phillycheeseman/particle/Proto Insert Two Layer/IMG_5750.jpeg

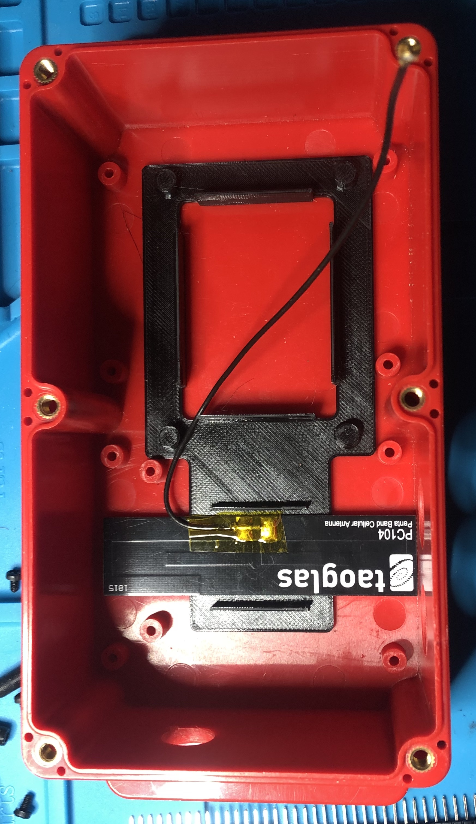
Proto Insert Two Layer/IMG_5750.jpeg
