phillycheeseman/particle/Proto Insert Two Layer/IMG_5751.jpeg

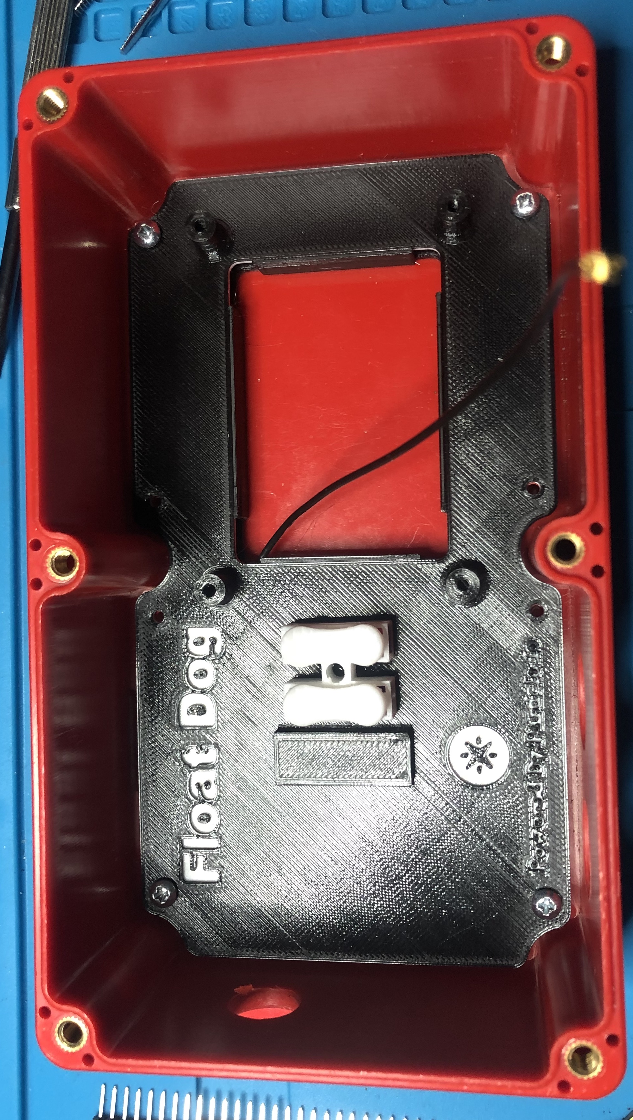
Proto Insert Two Layer/IMG_5751.jpeg
