phillycheeseman/particle/Proto Insert Two Layer/IMG_5753.jpeg

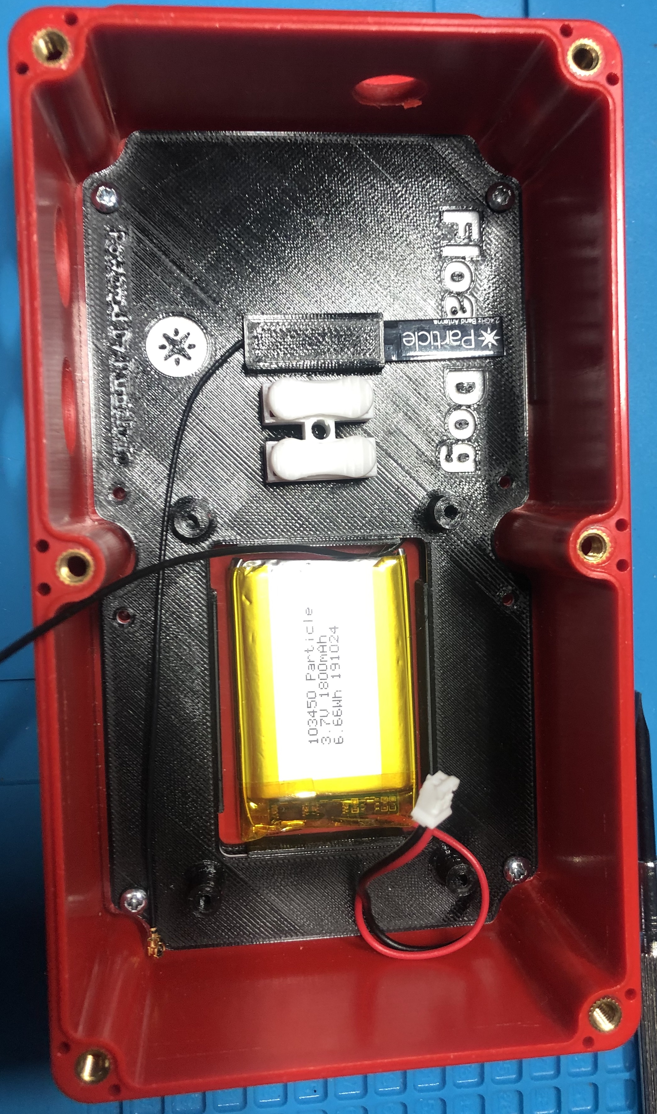
Proto Insert Two Layer/IMG_5753.jpeg
