phillycheeseman/particle/Proto Insert Two Layer/IMG_5755.jpeg

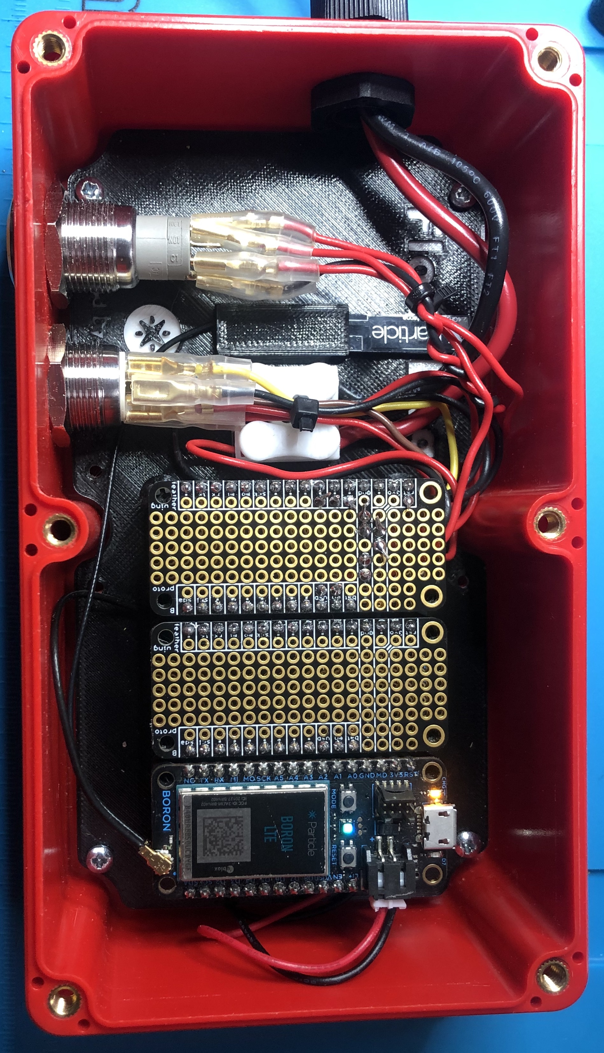
Proto Insert Two Layer/IMG_5755.jpeg
