phillycheeseman/particle/Proto Insert Two Layer/IMG_5757.jpeg

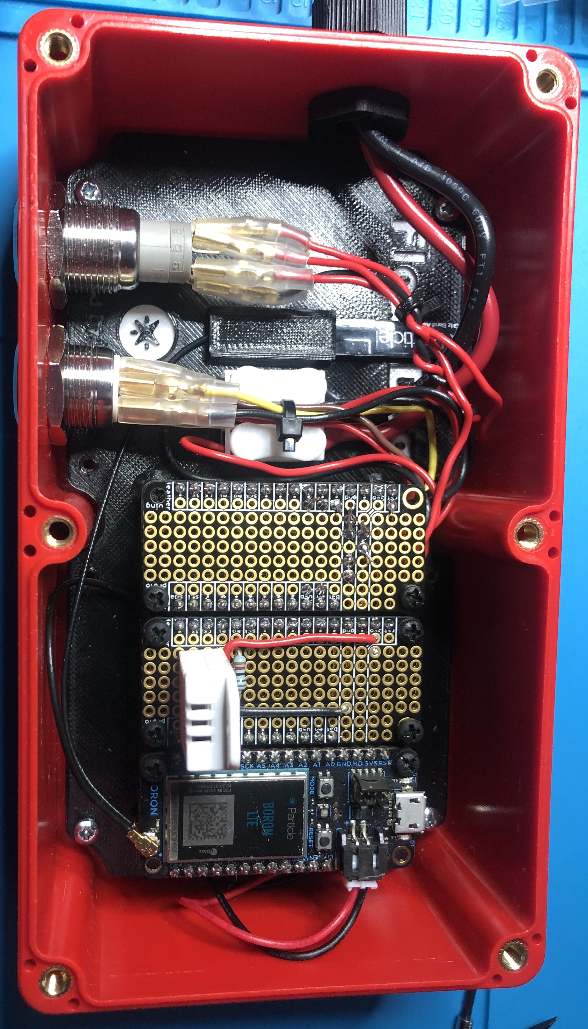
Proto Insert Two Layer/IMG_5757.jpeg
