phillycheeseman/particle/Proto Insert v14/IMG_5618.jpeg

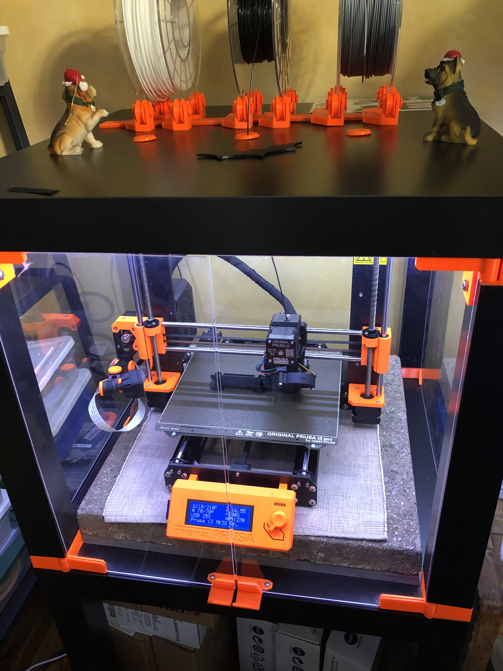
Proto Insert v14/IMG_5618.jpeg
