phillycheeseman/particle/Proto Insert v14/IMG_5620.jpeg

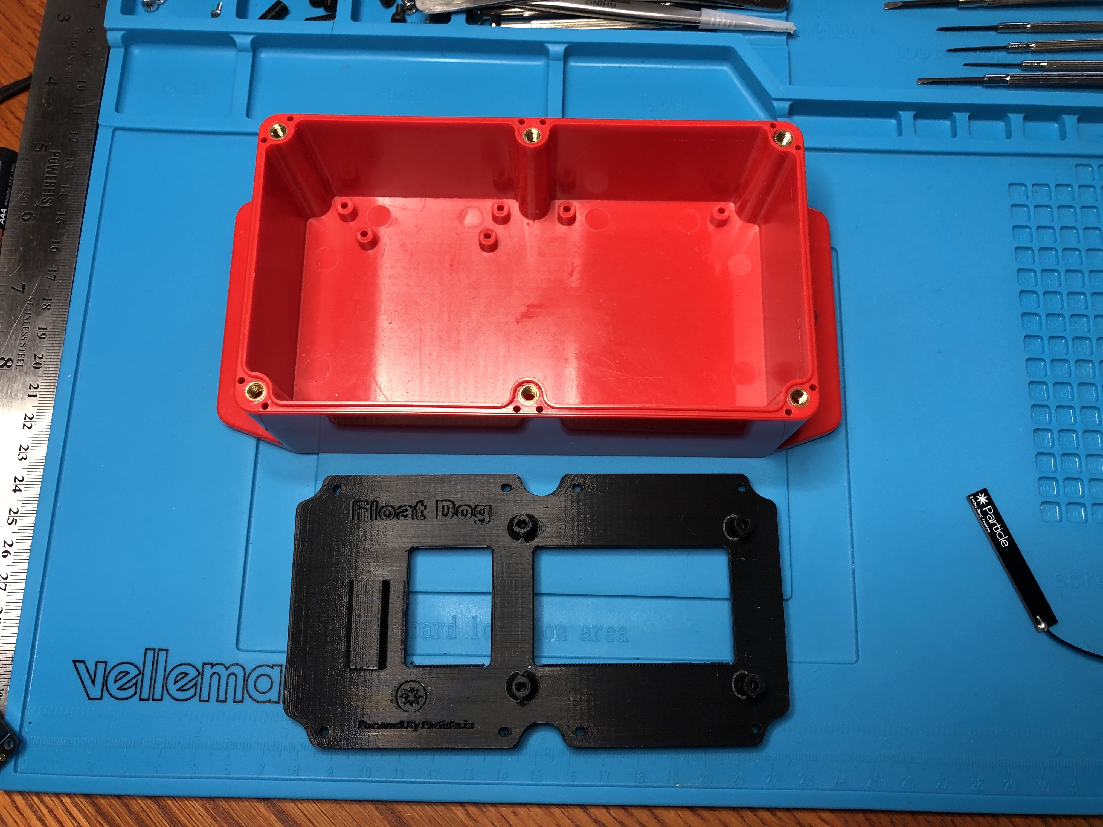
Proto Insert v14/IMG_5620.jpeg
