phillycheeseman/particle/Proto Insert v14/IMG_5621.jpeg

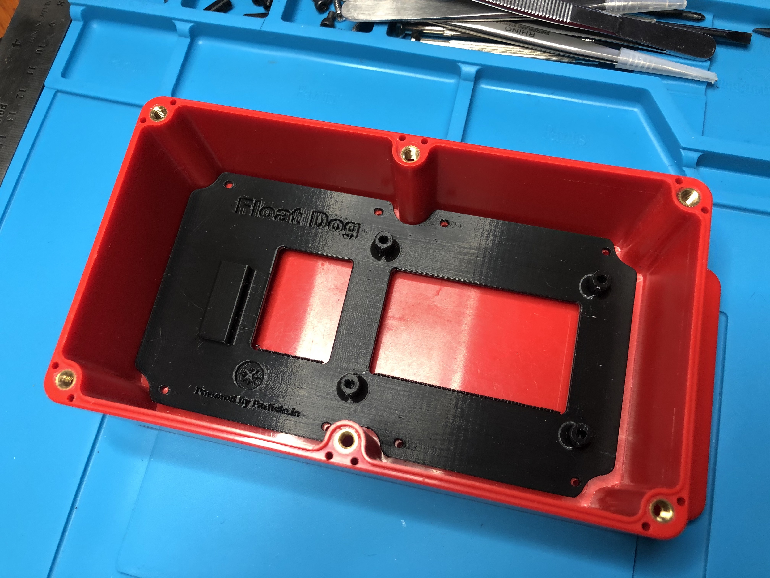
Proto Insert v14/IMG_5621.jpeg
