phillycheeseman/particle/Proto Insert v14/IMG_5622.jpeg

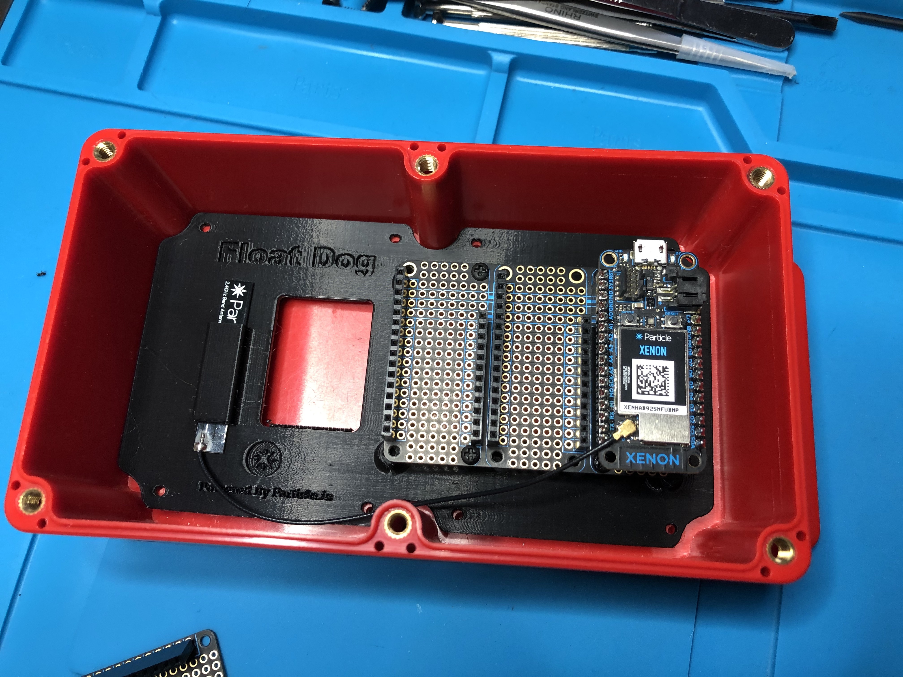
Proto Insert v14/IMG_5622.jpeg
