phillycheeseman/particle/Proto Insert v14/IMG_5623.jpeg

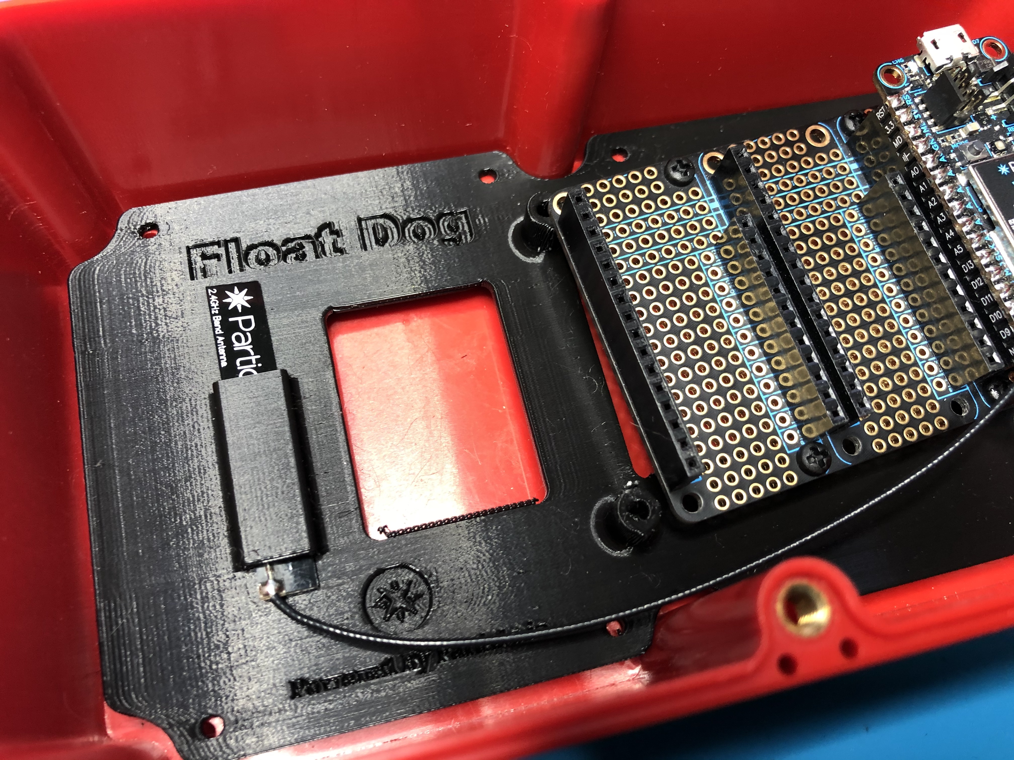
Proto Insert v14/IMG_5623.jpeg
