phillycheeseman/particle/Proto Insert v14/IMG_5625.jpeg

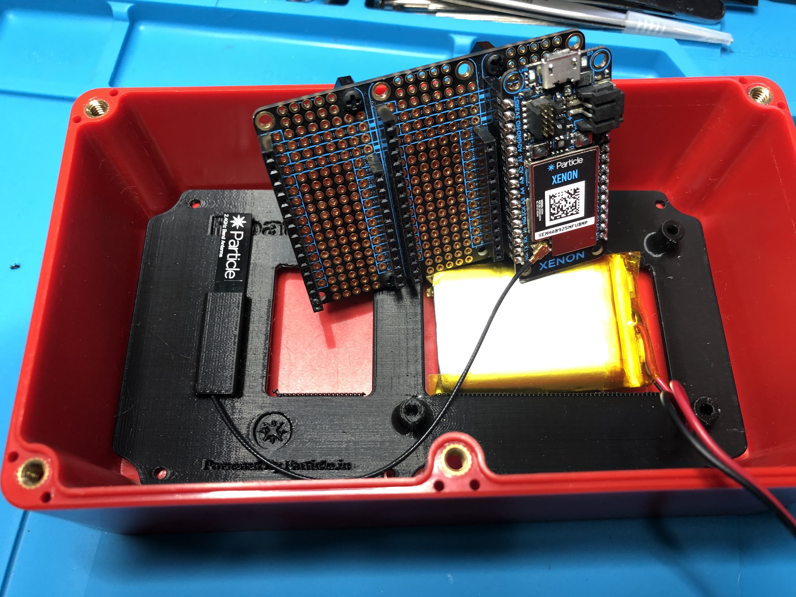
Proto Insert v14/IMG_5625.jpeg
