phillycheeseman/particle/Standoff Spacer/IMG_5627.jpeg

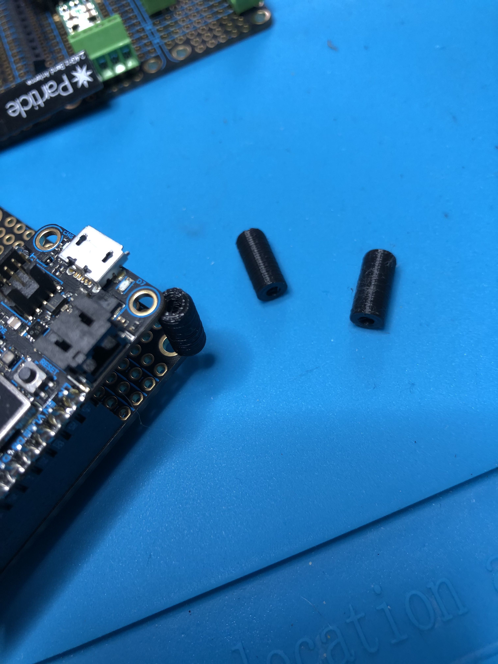
Standoff Spacer/IMG_5627.jpeg
